fl0m0/SCuSA/doc/img/binding_posts00.jpg

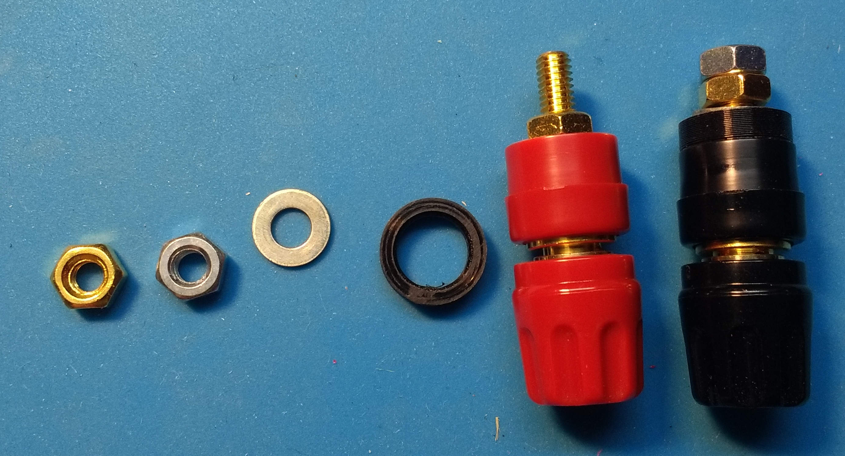
doc/img/binding_posts00.jpg
