fl0m0/SCuSA/doc/img/bottom_with_battery.jpg

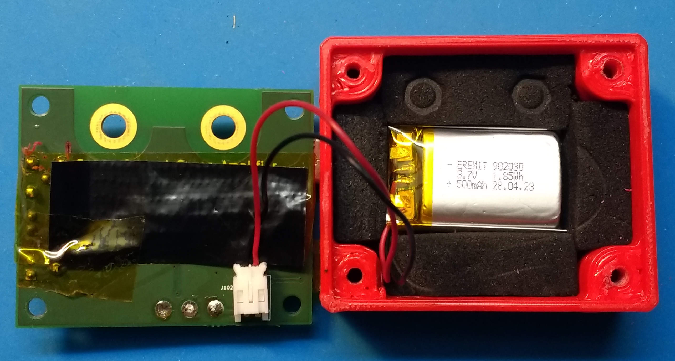
doc/img/bottom_with_battery.jpg
