fl0m0/SCuSA/doc/img/IMG_20230816_184149688.jpg

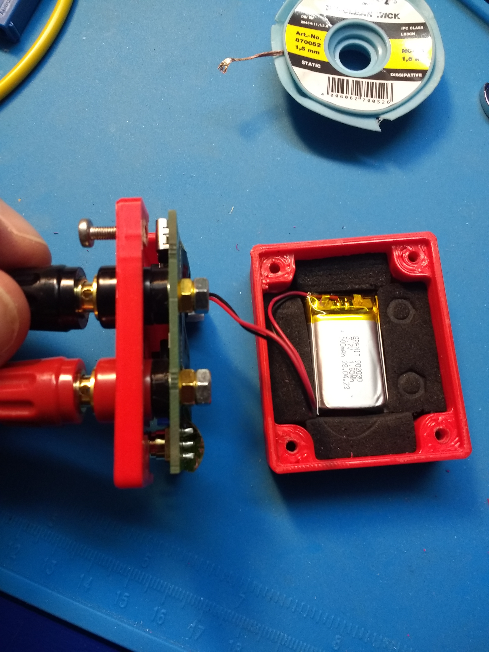
doc/img/IMG_20230816_184149688.jpg
