fl0m0/SCuSA/sim/Filter/Filter.asc

C1: cap; 4.7µ
C2: cap; 4.7µ
L1: WE-CBF
V1: voltage; ""; AC 1; Rser=50m
Named nets: 0, in, out
.ac dec 100 1 10Meg
