fl0m0/SCuSA/sim/Amplifier/VOffset_Filter.asc

C1: cap; 2.2µ
C2: cap; 1µ
L2: WE-CBF
R1: res; 0.1
V1: voltage; ""; AC 1
Named nets: 0, out
.ac dec 100 1 200Meg
