fl0m0/SCuSA/sim/Amplifier/Amplifier.asc

I1: current; PULSE(-1.8 3 0 0.1m 0.1m 1m 2m)
R1: res; 50m
R2: res; {Rpot*alpha}
R3: res; {Rpot*(1-alpha)}
U1: AD8418A
V1: voltage; 3.3
V3: voltage; 1
V4: voltage; -2
Named nets: 0, 3V3, out, ref, v-
.tran 10m
Top plot pane shows error.
.param Rpot = 10k
.param alpha = 0.621
