fl0m0/SCuSA/sim/Amplifier/Amplifier2.asc

I1: current; PULSE(0 1 0 0.1m 0.1m 0.2m 0.4m)
Q1: npn; 2N3904
R1: res; 200
R2: res; 2k
R3: res; 0.2
U1: LT1637
V1: voltage; 3
V2: voltage; 3
Named nets: 0, out, in, sense+, sense-
.tran 0.8m
